jrhahn/rs-smarthome-nodes/cad/export/wohnzimmer_lid.step

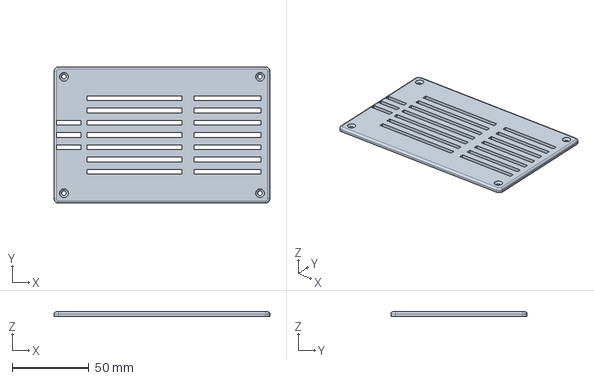
[picture p15: CAD file, 2026-09-13]
cad/export/wohnzimmer_lid.step
141.0 x 89.0 x 3.00 mm
