jrhahn/rs-smarthome-nodes/cad/export/wohnzimmer_tray.step

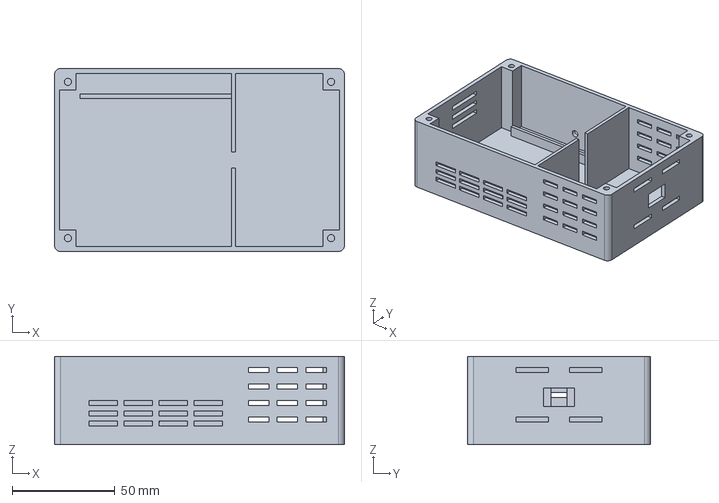
[picture p16: CAD file, 2026-09-13]
cad/export/wohnzimmer_tray.step
141.0 x 89.0 x 43.0 mm
