jrhahn/rs-smarthome-nodes/cad/export/climate_lid.step

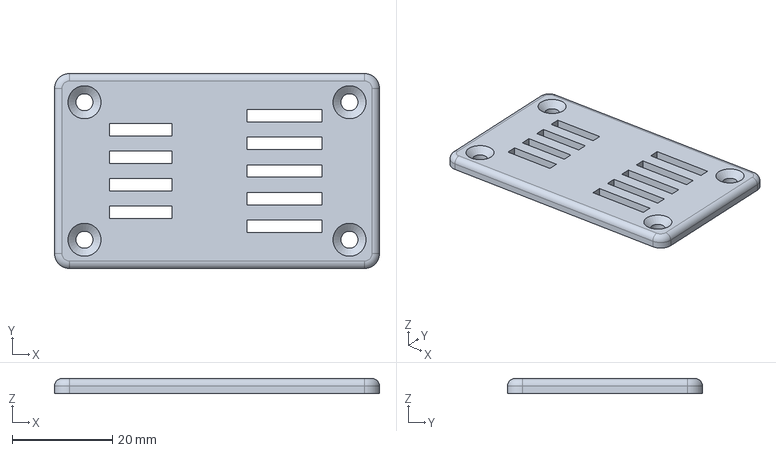
[picture p17: CAD file, 2026-09-13]
cad/export/climate_lid.step
65.0 x 39.0 x 3.00 mm
