jrhahn/rs-smarthome-nodes/cad/export/climate_tray.step

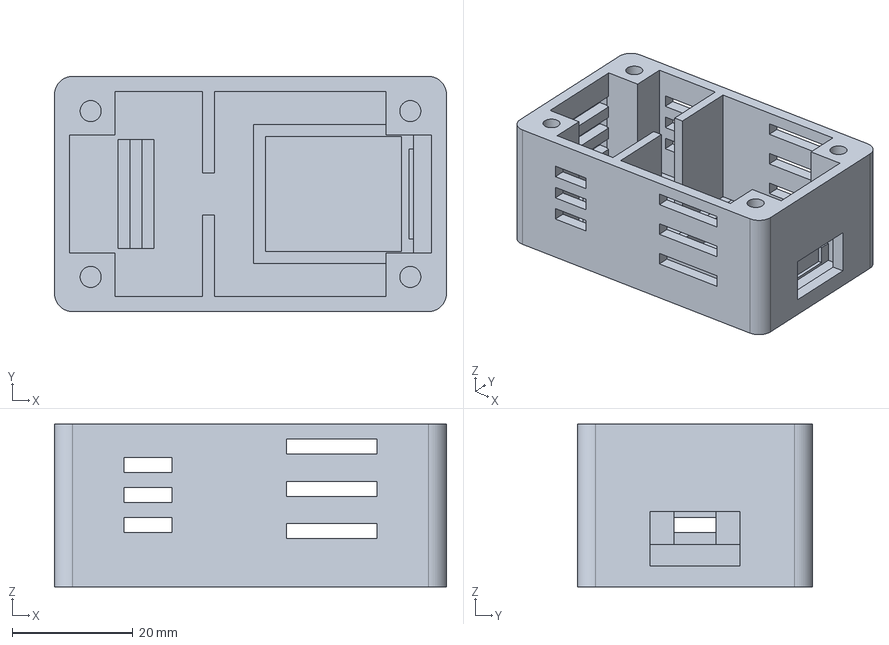
[picture p18: CAD file, 2026-09-13]
cad/export/climate_tray.step
65.0 x 39.0 x 27.0 mm
