jrhahn/rs-smarthome-nodes/src/state.rs

//! Tiny persistent state kept in RTC fast RAM.
//!
//! The firmware polls the scale by cold-booting out of deep sleep on a short
//! interval, so plain statics (in regular RAM) are wiped on every wake. The
//! tare baseline and the presence edge must instead survive across deep sleep,
//! which is exactly what `#[ram(unstable(rtc_fast, persistent))]` gives us: the startup
//! code leaves the region alone instead of zeroing it.
//!
//! **Nothing here may depend on the region being cleared when power is
//! removed.** Discovery used to: it was gated on a "have I announced yet" bit,
//! on the assumption that a cold power-on zeroes RTC RAM. On 2026-09-09 a
//! `wohnzimmer` node had its USB unplugged for several seconds and came back
//! with the bit still set, so its four SDS011 entities stayed unannounced
//! through a reflash, a reset *and* that power cycle — the readings were on the
//! broker the whole time with nothing in Home Assistant to receive them. The
//! board's rails evidently decay slower than the RTC domain forgets.
//!
//! So `FLAGS == 0` is a hint, not a guarantee. See [`discovery_tag`] for the
//! shape that stays correct when the hint is wrong.

use esp_hal::ram;

use crate::sensors::scale;

/// Last known empty-house reading, in raw HX711 ticks.
#[ram(unstable(rtc_fast, persistent))]
static mut BASELINE: i32 = 0;

/// Packed status bits; see `FLAG_*`.
#[ram(unstable(rtc_fast, persistent))]
static mut FLAGS: u32 = 0;

/// Empty-house idle wake-ups accumulated since the last publish. Drives the
/// periodic heartbeat: once it reaches `Config::heartbeat_wakes()` the firmware
/// publishes temperature + weight even without a visitor, then resets it. Any
/// real publish (bird arrived / left) also resets it, so the heartbeat clock
/// restarts from the last time Home Assistant already got a fresh reading.
#[ram(unstable(rtc_fast, persistent))]
static mut IDLE_WAKES: u32 = 0;

/// Consecutive rounds a load has been on the scale, for the stuck-load bound
/// in [`crate::presence::STUCK_AFTER_SECS`]. Reset by an arrival or a
/// departure, so it only ever counts one uninterrupted stretch.
#[ram(unstable(rtc_fast, persistent))]
static mut PRESENT_ROUNDS: u32 = 0;

/// Consecutive rounds the reading has sat in `Decision::Unexplained`, for the
/// recovery bound in [`crate::presence::UNEXPLAINED_ADOPT_AFTER_SECS`]. Reset
/// by every other verdict, so it only ever counts one uninterrupted stretch —
/// the same discipline as [`PRESENT_ROUNDS`], and for the same reason: an
/// occasional odd reading between quiet ones is not a stuck baseline.
#[ram(unstable(rtc_fast, persistent))]
static mut UNEXPLAINED_ROUNDS: u32 = 0;

/// A coarse wall clock in milliseconds, kept across deep sleep as a pair of
/// words because RTC RAM is addressed in `u32`.
///
/// Not read from any counter. It is *re-anchored* by every successful NTP sync
/// -- which happens on every publish round, so at most ten minutes apart -- and
/// between anchors it simply accrues the sleep intervals the node asked for.
/// Bridging ten minutes that way is accurate to a few seconds, where reading
/// the RTC counter would have meant reaching into esp-hal's clock internals for
/// no better answer.
///
/// Zero means "never synced", and readers must treat it as unknown rather than
/// as 1970. This is not a second timestamp source: `clock` explains why
/// stamping a reading from a drifting clock is worse than not stamping it, and
/// that argument stands. The only consumer is the night cadence, which asks an
/// hour-wide question and tolerates minutes of error.
#[ram(unstable(rtc_fast, persistent))]
static mut CLOCK_MS_LO: u32 = 0;
#[ram(unstable(rtc_fast, persistent))]
static mut CLOCK_MS_HI: u32 = 0;

/// Digest of the discovery messages last successfully announced from this
/// board; see [`crate::discovery::announcement_tag`]. Zero means "nothing".

#[ram(unstable(rtc_fast, persistent))]
static mut DISCOVERY_TAG: u32 = 0;

/// Visits counted since the board last lost power entirely.
///
/// Counted at the *arrival*, not at the publish, which is the whole point of
/// keeping it here rather than deriving it in Home Assistant: state topics go
/// out at QoS0 without retain, and `presence_publish_allowed` deliberately
/// drops arrivals that fall inside the 60 s rate limit. Both would undercount,
/// silently, and a bird that comes back twice in half a minute is two visits.
///
/// RTC RAM rather than the flash blob on purpose. A visit is a frequent event —
/// 75 of them on 2026-09-11 — and a flash write means erasing a sector, so
/// counting in flash would spend the sector's endurance on nothing. Losing the
/// total when the cell is swapped is the accepted cost: the entity is
/// `total_increasing`, and Home Assistant treats a drop to zero as a counter
/// reset rather than as negative consumption, so the long-term history it has
/// already recorded survives the board forgetting.
#[ram(unstable(rtc_fast, persistent))]
static mut VISIT_COUNT: u32 = 0;

/// Companion to [`VISIT_COUNT`], holding it XORed with
/// [`scale::VISITS_MAGIC`]. The pair is what makes the counter survivable: a
/// word that has just been added to the firmware comes up holding leftover
/// memory, and a reflash is not a cold boot, so there is no moment at which
/// zeroing it would have been reliable. See that constant for the full story.
#[ram(unstable(rtc_fast, persistent))]
static mut VISIT_CHECK: u32 = 0;

/// Set once the baseline has been tared at least once.
const FLAG_INIT: u32 = 1 << 0;
/// Set while weight is above the presence threshold (edge detection).
const FLAG_PRESENT: u32 = 1 << 1;
/// Set at the end of the first boot of a power cycle. RTC RAM is wiped by a
/// cold power-on but survives deep sleep, so an unset flag means "the board was
/// just plugged in", which is the moment someone might be waiting at the serial
/// console.
///
/// It survives a **reflash** too — verified on hardware 2026-08-19, an
/// `espflash flash` plus the reset it performs left these flags standing. Only
/// removing power clears them. So a board that has already booted once will not
/// re-open the console window just because you flashed it.
const FLAG_BOOTED: u32 = 1 << 3;
/// Set by [`crate::panic_reset`] on its way out, so the boot that follows can
/// say *why* it restarted itself. Without it a panic is reported as a plain
/// software reset, which is also what an over-the-air update looks like -- and
/// the two want very different reactions.
const FLAG_PANICKED: u32 = 1 << 4;
/// Set while a battery node is parked on a low cell; see
/// [`crate::battery::should_park`]. Bit 2 is skipped: RTC RAM survives a
/// reflash, so a bit an older image used could still be standing.
const FLAG_PARKED: u32 = 1 << 5;

/// Whether this node is parked on a low cell.
pub fn parked() -> bool {
    flags() & FLAG_PARKED != 0
}

/// Record whether it is.
pub fn set_parked(value: bool) {
    set_flag(FLAG_PARKED, value);
}

/// Whether the last restart was this firmware giving up on itself.
pub fn panicked() -> bool {
    flags() & FLAG_PANICKED != 0
}

/// Record that it was, or that it has been reported.
pub fn set_panicked(value: bool) {
    set_flag(FLAG_PANICKED, value);
}

fn flags() -> u32 {
    // Single-word reads/writes of a `Persistable` primitive; no other execution
    // context touches these, so a raw read/write is sufficient.
    unsafe { core::ptr::addr_of!(FLAGS).read() }
}

fn set_flags(value: u32) {
    unsafe { core::ptr::addr_of_mut!(FLAGS).write(value) }
}

fn set_flag(bit: u32, on: bool) {
    let updated = if on { flags() | bit } else { flags() & !bit };
    set_flags(updated);
}

/// The persisted empty-house baseline.
pub fn baseline() -> i32 {
    unsafe { core::ptr::addr_of!(BASELINE).read() }
}

/// Replace the persisted baseline.
pub fn set_baseline(value: i32) {
    unsafe { core::ptr::addr_of_mut!(BASELINE).write(value) }
}

/// Whether a baseline has ever been established (false only on the first boot).
pub fn is_initialised() -> bool {
    flags() & FLAG_INIT != 0
}

/// Mark the baseline as established.
pub fn mark_initialised() {
    set_flag(FLAG_INIT, true);
}

/// Whether the previous cycle saw weight on the scale.
pub fn bird_present() -> bool {
    flags() & FLAG_PRESENT != 0
}

/// Record whether weight is currently on the scale.
pub fn set_bird_present(present: bool) {
    set_flag(FLAG_PRESENT, present);
}

/// The digest of the discovery messages last announced from this board, or 0.
///
/// Compared against [`crate::discovery::announcement_tag`] rather than being a
/// boolean, because *any* difference in what Home Assistant should know has to
/// re-announce: a sensor switched on in [`crate::node`] and reflashed, a
/// changed `expire_after`, or RTC RAM that survived a power cycle holding a
/// value from before all of that.
///
/// The boolean it replaces could only ever answer "done", which is precisely
/// the answer that cannot be checked — and it was wrong for six days on the
/// living-room node (see the module note). A digest is checkable: if it does
/// not match what this image would send, the announce happens again, and a
/// stale or garbage word fails to match all by itself.
pub fn discovery_tag() -> u32 {
    unsafe { core::ptr::addr_of!(DISCOVERY_TAG).read() }
}

/// Record the digest of the messages that just went out.
pub fn set_discovery_tag(tag: u32) {
    unsafe { core::ptr::addr_of_mut!(DISCOVERY_TAG).write(tag) }
}

/// How many consecutive rounds a load has been on the scale.
pub fn present_rounds() -> u32 {
    unsafe { core::ptr::addr_of!(PRESENT_ROUNDS).read() }
}

/// Replace the consecutive-load counter.
pub fn set_present_rounds(value: u32) {
    unsafe { core::ptr::addr_of_mut!(PRESENT_ROUNDS).write(value) }
}

/// Anchor the coarse clock to a freshly synced wall time.
pub fn set_clock_ms(millis: u64) {
    unsafe {
        core::ptr::addr_of_mut!(CLOCK_MS_LO).write(millis as u32);
        core::ptr::addr_of_mut!(CLOCK_MS_HI).write((millis >> 32) as u32);
    }
}

/// Carry the coarse clock forward by a stretch the node is about to spend, or
/// just spent. A no-op while the clock is unknown -- advancing a zero would
/// invent a time in 1970 and then keep it.
pub fn advance_clock_ms(millis: u64) {
    if let Some(now) = clock_ms() {
        set_clock_ms(now.saturating_add(millis));
    }
}

/// The coarse wall clock, or `None` if it was never set or has stopped being
/// believable.
pub fn clock_ms() -> Option<u64> {
    let millis = unsafe {
        (core::ptr::addr_of!(CLOCK_MS_HI).read() as u64) << 32
            | core::ptr::addr_of!(CLOCK_MS_LO).read() as u64
    };
    crate::clock::is_plausible(millis).then_some(millis)
}

/// How many consecutive rounds the reading has been unexplained.
/// How many consecutive rounds the reading has been unexplained.
pub fn unexplained_rounds() -> u32 {
    unsafe { core::ptr::addr_of!(UNEXPLAINED_ROUNDS).read() }
}

/// Replace the unexplained-streak counter.
pub fn set_unexplained_rounds(value: u32) {
    unsafe { core::ptr::addr_of_mut!(UNEXPLAINED_ROUNDS).write(value) }
}

/// Visits counted since the last full power loss, or zero if the stored pair
/// does not agree -- which is what leftover RTC memory looks like.
pub fn visit_count() -> u32 {
    let value = unsafe { core::ptr::addr_of!(VISIT_COUNT).read() };
    let check = unsafe { core::ptr::addr_of!(VISIT_CHECK).read() };
    scale::visits_from_pair(value, check)
}

/// Replace the visit counter, writing both halves of the pair so the next read
/// trusts it. Every caller that wants to *record* a visit wants [`count_visit`].
pub fn set_visit_count(value: u32) {
    unsafe {
        core::ptr::addr_of_mut!(VISIT_COUNT).write(value);
        core::ptr::addr_of_mut!(VISIT_CHECK).write(scale::visits_check(value));
    }
}

/// Record one arrival. Saturating, so a board left running for years reports a
/// stuck maximum rather than wrapping to zero and looking like a fresh install.
pub fn count_visit() {
    set_visit_count(visit_count().saturating_add(1));
}

/// Idle wake-ups accumulated since the last publish.
pub fn idle_wakes() -> u32 {
    unsafe { core::ptr::addr_of!(IDLE_WAKES).read() }
}

/// Overwrite the idle wake-up counter (e.g. bump on an empty poll, or reset to
/// zero right after a publish).
pub fn set_idle_wakes(value: u32) {
    unsafe { core::ptr::addr_of_mut!(IDLE_WAKES).write(value) }
}

/// Is this the first boot since the board was **powered up** — power actually
/// removed and reapplied — rather than a wake from deep sleep? A reflash or a
/// reset does not count; see [`FLAG_BOOTED`].
pub fn is_cold_boot() -> bool {
    flags() & FLAG_BOOTED == 0
}

/// Record that this power cycle has booted once; every later wake sees it.
pub fn mark_booted() {
    set_flag(FLAG_BOOTED, true);
}

// --- Reset diagnostics -------------------------------------------------------

/// Reset cause of the most recent boot that was **not** an ordinary deep-sleep
/// wake, as the raw `SocResetReason` discriminant. Zero until one happens.
///
/// Latched rather than read live because the two do not line up in time: a
/// battery node wakes some hundreds of times between publishes, so the boot
/// that carries the interesting cause is almost never the boot that gets to
/// talk to the broker. Holding it here means the next publish carries it.
///
/// RTC RAM is exactly the right store for this. A watchdog reset, a brownout
/// and a software reset all leave it intact, so the evidence survives the event
/// it describes; only removing power clears it, and that is a power-on reset —
/// which this then records as itself.
#[ram(unstable(rtc_fast, persistent))]
static mut RESET_REASON: u32 = 0;

/// How many such resets since power was last removed. One alone is ambiguous;
/// a count climbing over days is a node rebooting in a loop nobody has noticed,
/// which is the failure this whole pair exists to make visible.
#[ram(unstable(rtc_fast, persistent))]
static mut RESET_COUNT: u32 = 0;

/// Says the words around it are ours rather than whatever the region held
/// before. See [`crate::reset_reason::EPOCH_TAG`] for why this is not optional.
#[ram(unstable(rtc_fast, persistent))]
static mut RESET_TAG: u32 = 0;

/// Consecutive joins the *stored* Wi-Fi credentials have been refused; see
/// [`crate::wifi::FALLBACK_AFTER`].
///
/// Here rather than in the connection task because a battery node cold-boots
/// every few seconds: a task local was reset before the threshold could ever be
/// reached, so the fallback never fired on the one node that hangs outdoors.
/// [`crate::reset_reason::latch`] clears it on a power-on, which is the
/// "another try" the original comment intended.
#[ram(unstable(rtc_fast, persistent))]
static mut JOIN_REFUSALS: u32 = 0;

/// Consecutive publish rounds that never reached the broker; see
/// [`crate::node::sleep_backoff_factor`].
///
/// Rounds rather than attempts, and that is why it is not [`JOIN_REFUSALS`]
/// read a second time: with an exponential join backoff a single failed round
/// now spends four or five refusals, so that counter measures how hard the
/// round tried and this one measures how many rounds went nowhere. Only the
/// second is a sane thing to stretch a sleep by.
#[ram(unstable(rtc_fast, persistent))]
static mut FAILED_ROUNDS: u32 = 0;

/// Record this boot's reset cause. Call once, early. A deep-sleep wake is the
/// steady state and is ignored, so what stays latched is the last thing that
/// was not routine.
pub fn note_reset(code: u32) {
    unsafe {
        // Cleared on the same two occasions `latch` clears `JOIN_REFUSALS`: a
        // region that was never ours holds whatever the last firmware left
        // there, and a power-on is somebody standing at the board. Letting
        // either survive would have the first round after it sleep at a
        // backoff earned by a previous run -- half an hour, on a battery node.
        if !reset_state_is_ours() || code == crate::reset_reason::POWER_ON {
            core::ptr::addr_of_mut!(FAILED_ROUNDS).write(0);
        }
        let (tag, count, latched, refusals) = crate::reset_reason::latch(
            core::ptr::addr_of!(RESET_TAG).read(),
            core::ptr::addr_of!(RESET_COUNT).read(),
            core::ptr::addr_of!(RESET_REASON).read(),
            core::ptr::addr_of!(JOIN_REFUSALS).read(),
            code,
        );
        core::ptr::addr_of_mut!(RESET_TAG).write(tag);
        core::ptr::addr_of_mut!(RESET_COUNT).write(count);
        core::ptr::addr_of_mut!(RESET_REASON).write(latched);
        core::ptr::addr_of_mut!(JOIN_REFUSALS).write(refusals);
    }
}

/// Consecutive refusals of the stored credentials, across sleeps. Zero if the
/// region is not ours, so a garbage read cannot fake a run of failures.
pub fn join_refusals() -> u32 {
    if !reset_state_is_ours() {
        return 0;
    }
    unsafe { core::ptr::addr_of!(JOIN_REFUSALS).read() }
}

/// Record the running total. Called by the connection task on each outcome.
pub fn set_join_refusals(value: u32) {
    unsafe { core::ptr::addr_of_mut!(JOIN_REFUSALS).write(value) }
}

/// Consecutive rounds that did not reach the broker, across sleeps. Zero if the
/// region is not ours, so a garbage read cannot stretch a sleep.
pub fn failed_rounds() -> u32 {
    if !reset_state_is_ours() {
        return 0;
    }
    unsafe { core::ptr::addr_of!(FAILED_ROUNDS).read() }
}

/// Record the running total. Called once per publish round, on each outcome.
pub fn set_failed_rounds(value: u32) {
    unsafe { core::ptr::addr_of_mut!(FAILED_ROUNDS).write(value) }
}

/// Whether the words hold a history of ours. False before [`note_reset`] has
/// run on a region that was never ours.
fn reset_state_is_ours() -> bool {
    unsafe {
        core::ptr::addr_of!(RESET_TAG).read() == crate::reset_reason::EPOCH_TAG
            && core::ptr::addr_of!(RESET_COUNT).read() <= crate::reset_reason::MAX_PLAUSIBLE_COUNT
    }
}

/// The latched cause, or zero if nothing but deep sleep has happened.
pub fn last_reset() -> u32 {
    if !reset_state_is_ours() {
        return 0;
    }
    unsafe { core::ptr::addr_of!(RESET_REASON).read() }
}

/// How many non-routine resets since power-on.
pub fn reset_count() -> u32 {
    if !reset_state_is_ours() {
        return 0;
    }
    unsafe { core::ptr::addr_of!(RESET_COUNT).read() }
}
