jrhahn/rs-smarthome-nodes/src/config.rs

//! Runtime configuration persisted in flash (NVS sector) and tunable live from
//! Home Assistant over retained MQTT.
//!
//! Historically the tuning knobs (`PRESENCE_THRESHOLD`, poll intervals) were
//! compile-time constants and the gram calibration (`offset` / `scale_factor`)
//! lived in the Home Assistant template. This module moves all of that onto the
//! controller so it can be changed **without reflashing**: HA publishes each
//! value to a retained `<namespace>/<node>/config/<key>` topic, the firmware reads them
//! whenever it is already online for a publish, and stores the result here.
//!
//! Persistence is a single fixed-layout blob in one 4 KiB flash sector, guarded
//! by a magic + version + CRC-32 so a blank or corrupt sector falls back to
//! [`Config::DEFAULT`]. RTC RAM ([`crate::state`]) is deliberately *not* used for
//! this: it is wiped on a cold power-on (battery swap), and calibration must
//! survive that.
//!
//! The blob encoding and [`Config::apply`] are pure and always compiled; only
//! the flash access itself sits behind the `hal` feature, so the layout and the
//! parsing can be unit-tested on the host (see the `tests` module below).

use core::time::Duration as CoreDuration;

#[cfg(feature = "hal")]
use embedded_storage::{ReadStorage, Storage};
use heapless::String;

use crate::sensors::{scd41, sds011};
use crate::solar;

/// Flash byte-offset of the config blob. Matches the `nvs` partition in
/// espflash's default table; we only touch the first sector of it.
const FLASH_OFFSET: u32 = 0x9000;

/// Second sector of the same partition, holding the node-identity override
/// (see [`crate::node`]). Deliberately a *separate* blob: provisioning a board
/// must never be able to disturb the calibration, and the identity is written
/// once in a board's life while the tuning changes all the time.
const NODE_OFFSET: u32 = 0xA000;

/// Third sector: the Wi-Fi credentials (see [`crate::wifi`]). Separate again,
/// and for a sharper reason than the others — this is the one blob whose loss
/// takes a board off the network entirely, so nothing else may share a sector
/// erase with it.
const WIFI_OFFSET: u32 = 0xB000;

/// `"BIRD"` little-endian — marks an initialised blob.
const MAGIC: u32 = 0x4449_5242;
/// Bump when the on-flash layout changes. A version this code does not know
/// reverts to defaults; the one version it does know how to read comes through
/// [`Config::from_bytes`]'s migration instead — see [`V5_LEN`].
const VERSION: u8 = 7;
/// Serialised length: magic(4) + version(1) + pad(3) + fourteen 4-byte fields + crc(4).
const BLOB_LEN: usize = 4 + 4 + 4 * 14 + 4;
/// Where version 6 ended — the twelve fields up to the tare anchor.
const V6_LEN: usize = 4 + 4 + 4 * 12 + 4;

/// Where version 5 ended: the same header and the first ten fields, then its own
/// CRC. Kept so a board that has been running since before the temperature
/// compensation existed keeps its calibration across the upgrade. `offset` and
/// `scale_factor` are measured against a known weight on a still scale, and
/// dropping them to defaults would turn every reading into plausible nonsense
/// until someone noticed and redid the procedure.
const V5_LEN: usize = 4 + 4 + 4 * 10 + 4;

/// All runtime-tunable settings. `f32` calibration fields are compared bitwise
/// for change detection, which is exactly what we want (a re-sent identical
/// value is a no-op and skips the flash write).
#[derive(Clone, Copy, PartialEq)]
pub struct Config {
    /// Raw HX711 reading corresponding to 0 g (the tare zero).
    pub offset: i32,
    /// Raw HX711 ticks per gram.
    pub scale_factor: f32,
    /// Weight, in grams, that counts as "a bird landed".
    pub threshold_grams: f32,
    /// Deep-sleep seconds between polls while the house is empty.
    pub idle_secs: u32,
    /// Deep-sleep seconds between publishes while a bird is present.
    pub active_secs: u32,
    /// Last numeric tare token seen, so a replayed one is not mistaken for a
    /// second press. `0` for the discovered button, which has no token (see
    /// [`Config::apply`]).
    pub tare_token: u32,
    /// When `false`, the firmware never deep-sleeps: it stays awake and keeps
    /// Wi-Fi up in a loop. Meant for bench testing on USB where deep sleep just
    /// churns the serial monitor. Only consulted on a node whose profile sleeps
    /// at all — a node on [`crate::node::PowerProfile::Mains`] stays awake
    /// regardless.
    pub deep_sleep: bool,
    /// Whether the lamp lights at all tonight, from Home Assistant's light
    /// entity. The twilight window and the cell still decide *when* and *how
    /// bright*; this only ever turns the whole evening off.
    pub lamp_enabled: bool,
    /// Home Assistant's brightness slider, 0..=255.
    ///
    /// A **factor on** [`crate::lamp::MAX_DUTY_PCT`], never a replacement for
    /// it: 255 means "as bright as the compiled ceiling allows", not "full
    /// duty". See the ceiling's own note for why that distinction is the whole
    /// point.
    pub lamp_brightness: u8,
    /// Seconds between periodic "heartbeat" publishes: even with no visitor, the
    /// firmware brings Wi-Fi up this often and publishes temperature + weight so
    /// Home Assistant keeps a fresh reading. Realised as a whole number of idle
    /// wake-ups (see [`Config::heartbeat_wakes`]).
    pub heartbeat_secs: u32,
    /// SCD41 temperature offset in hundredths of °C — the self-heating the
    /// sensor subtracts from both its temperature *and* its humidity output.
    /// Stored in hundredths rather than as an `f32` because it is a calibration
    /// figure read off a comparison, not a computed quantity, and 0.01 °C is
    /// already four times finer than the register resolves. Only consulted on a
    /// node carrying an SCD41 (see [`crate::sensors::scd41`]).
    pub scd41_offset_centi: i32,
    /// Hygroscopic-growth constant κ in hundredths, for the SDS011's humidity
    /// correction (see [`crate::sensors::sds011::compensate`]). Tunable at all
    /// because the right value is a property of the aerosol in *your* rooms
    /// rather than of the sensor; `0` switches the correction off. Only
    /// consulted on a node whose SDS011 slot is compensated.
    pub sds011_kappa_centi: u32,
    /// How far the scale's zero moves with air temperature, in hundredths of a
    /// gram per kelvin. `0` — the default — switches the correction off.
    ///
    /// Signed, because which way the zero goes depends on how the mount is
    /// built, and on the terrace node it goes *down* as it cools. Tunable at
    /// all for the same reason as the SDS011's κ: the figure is a property of
    /// *this* mount rather than of the load cell. On a 1 kg cell the terrace
    /// node measured about 10 g/K, some twenty times a decent cell's own
    /// zero-TC spec, which is what says the strain is in the printed clamps
    /// and not in the steel.
    pub temp_coeff_centi: i32,
    /// Air temperature at the last tare, in tenths of a degree, or
    /// [`TARE_TEMP_UNKNOWN`] if no tare has recorded one.
    ///
    /// The correction needs an anchor, and the tare is the only moment the
    /// node knows the zero is right. Storing the temperature *of that moment*
    /// beside `offset` makes the pair describe one physical state, the same
    /// argument that made `retare` re-anchor the presence baseline. It also
    /// makes the feature roll out safely: until a tare has happened under the
    /// new firmware there is no anchor, and the correction stays off however
    /// the coefficient is set.
    pub tare_temp_tenths: i32,
    /// Deep-sleep seconds between polls during the night window, or `0` to poll
    /// at the ordinary [`Config::idle_secs`] around the clock.
    ///
    /// The cheapest saving this node has left, because it costs nothing that
    /// matters: birds do not feed in the dark, and every wake between dusk and
    /// dawn is the node confirming that nothing is happening. At the measured
    /// 6 s cycle and 1 s awake, a night at 5 s is some 5 400 wake-ups for no
    /// information at all.
    ///
    /// It lengthens the *idle* cadence only. An active interval means a visitor
    /// is being watched, which by definition is not the quiet night this is
    /// about.
    pub night_idle_secs: u32,
    /// Daylight kept clear at each end of the night window, in minutes.
    ///
    /// The window itself is not stored: it is sunset and sunrise for the day,
    /// from [`crate::solar`], so it follows the season without anyone editing
    /// it twice a year. This is the one knob over it — how long after dusk the
    /// node stops looking, and how long before dawn it starts again.
    pub night_margin_min: u32,
}

/// `tare_temp_tenths` when no tare has recorded a temperature.
///
/// A sentinel rather than an `Option` because the blob stores fixed-width
/// fields, and `i32::MIN` is -214 748 364.8 °C — outside anything the SHT31 can
/// report by a wide margin, and outside anything that could arrive from a
/// half-written sector that still passed the CRC.
pub const TARE_TEMP_UNKNOWN: i32 = i32::MIN;

/// The largest zero drift the correction will accept, in hundredths of a gram
/// per kelvin. Generous — the terrace mount sits at a tenth of it — but finite,
/// so a mistyped slider cannot turn a few degrees into kilograms.
pub const MAX_TEMP_COEFF_CENTI: i32 = 20_000;

impl Config {
    /// Factory defaults, used on first boot or a corrupt sector. Chosen to match
    /// the historical compile-time constants, except the threshold which is now
    /// expressed in grams.
    pub const DEFAULT: Config = Config {
        offset: 8_388_608, // mid-scale; overwritten by the first tare / calibration
        scale_factor: 420.0,
        threshold_grams: 10.0,
        idle_secs: 2,
        active_secs: 10,
        tare_token: 0,
        // Sleeping by default, for every profile that sleeps at all. A node
        // that stays awake ignores the flag entirely (see `node::PowerProfile`),
        // so this needs no per-node value — which also keeps `DEFAULT` a plain
        // constant now that the node identity is resolved at runtime from flash.
        deep_sleep: true,
        // On and as bright as the ceiling permits. Neither is persisted in the
        // blob — see `the_lamp_knobs_are_deliberately_not_persisted`.
        lamp_enabled: true,
        lamp_brightness: 255,
        heartbeat_secs: 600, // 10 min
        // The sensor's own power-on value, so an un-calibrated node behaves
        // exactly as it did before this knob existed.
        scd41_offset_centi: scd41::DEFAULT_OFFSET_CENTI,
        // Conservative end of the published range for indoor aerosol; see the
        // constant's own note on why this is a starting point, not a
        // calibration.
        sds011_kappa_centi: sds011::KAPPA_CENTI_DEFAULT,
        // Off. The coefficient belongs to one physical mount, so there is no
        // sensible fleet-wide value to guess at, and a wrong one is worse than
        // none: it would move a zero that was not drifting.
        temp_coeff_centi: 0,
        tare_temp_tenths: TARE_TEMP_UNKNOWN,
        // Off, like every other opt-in here: a node whose clock has never
        // been set must behave exactly as it did before this existed.
        night_idle_secs: 0,
        // Half an hour. Birds feed into dusk and start again before full
        // light, so the window is the inside of the night rather than all of
        // it; see `solar::is_night` for why the two errors do not cost the
        // same.
        night_margin_min: 30,
    };

    /// The presence threshold expressed in raw HX711 ticks, i.e. what `main`
    /// compares the load delta against. Clamped to at least 1 tick so a bad
    /// (zero/negative) calibration can never make everything look "present".
    pub fn threshold_ticks(&self) -> i32 {
        let ticks = self.threshold_grams * self.scale_factor;
        if ticks.is_finite() && ticks >= 1.0 {
            ticks as i32
        } else {
            1
        }
    }

    /// The idle cadence for `hour`, which is the night one inside the window.
    ///
    /// `None` means the node does not know what time it is -- no successful NTP
    /// sync since it last lost power -- and then it polls at the day cadence.
    /// That is the safe direction to be wrong in: it costs current, where the
    /// other way costs visitors.
    pub fn idle_interval_at(&self, now_ms: Option<u64>) -> CoreDuration {
        match now_ms {
            Some(ms)
                if self.night_idle_secs > 0
                    && solar::is_night(
                        solar::minute_of_day(ms),
                        solar::day_of_year(ms),
                        self.night_margin_min,
                    ) =>
            {
                CoreDuration::from_secs(self.night_idle_secs.max(1) as u64)
            }
            _ => self.idle_interval(),
        }
    }

    pub fn idle_interval(&self) -> CoreDuration {
        CoreDuration::from_secs(self.idle_secs.max(1) as u64)
    }

    pub fn active_interval(&self) -> CoreDuration {
        CoreDuration::from_secs(self.active_secs.max(1) as u64)
    }

    /// The heartbeat period as a sleep duration. A battery node **without** a
    /// load cell has no presence logic and therefore nothing to poll for, so
    /// every wake-up is already a full publish; this is what it sleeps between
    /// them, rather than the load-cell [`Config::idle_interval`].
    pub fn heartbeat_interval(&self) -> CoreDuration {
        CoreDuration::from_secs(self.heartbeat_secs.max(1) as u64)
    }

    /// Number of idle wake-ups that make up one heartbeat period: after this
    /// many empty-poll cycles, bring Wi-Fi up and publish temperature + weight
    /// even without a visitor. At least 1, so a misconfigured (tiny) interval
    /// still fires every cycle rather than never.
    /// Whole wake-ups of `wake_secs` before the next heartbeat is due.
    ///
    /// Takes the interval rather than reading [`Config::idle_secs`], because
    /// since the night cadence exists those two are not the same number. A
    /// heartbeat counted in day-length rounds while the node sleeps night-length
    /// ones stretches by exactly their ratio: 120 rounds is ten minutes at 5 s
    /// and **ten hours** at 300 s. The node would go dark from dusk to dawn --
    /// no temperature, no battery, no weight -- which is indistinguishable from
    /// the outage this fleet spent two days chasing in September 2026.
    pub fn heartbeat_wakes_at(&self, wake_secs: u32) -> u32 {
        (self.heartbeat_secs / wake_secs.max(1)).max(1)
    }

    /// Seconds this round will sleep, night cadence included. The one number
    /// every other "seconds to rounds" conversion in a round has to agree with.
    pub fn wake_secs_at(&self, now_ms: Option<u64>) -> u32 {
        self.idle_interval_at(now_ms).as_secs() as u32
    }

    /// Whether a `tare` payload is a fresh press rather than an echo of one
    /// already acted on, remembering the token if it is.
    ///
    /// Two ways to ask for a re-zero, both landing here:
    ///
    /// * a discovered Home Assistant *button*, whose payload is a constant —
    ///   every press looks identical, so the caller deletes the retained
    ///   message once it has acted on it;
    /// * a numeric token (the older automation that published a timestamp),
    ///   where a repeat of the same value is a replay, not a new press.
    ///   Remembering the token means that keeps working, and doubles as a
    ///   backstop if the button's retained message ever fails to clear.
    ///
    /// Split out of [`Config::apply`] so the decision stays host-tested while
    /// the measurement that follows it lives where the load cell is.
    pub fn tare_press_is_new(&mut self, value: &str) -> bool {
        if value.is_empty() {
            return false;
        }
        let token = value.parse::<u32>().unwrap_or(0);
        if token != 0 && token == self.tare_token {
            return false;
        }
        self.tare_token = token;
        true
    }

    /// How many raw ticks of the current reading are the mount expanding rather
    /// than something landing on it — the number to subtract before anything
    /// else looks at the sample.
    ///
    /// Returned in *ticks* rather than grams so the correction lands upstream of
    /// everything: the gram conversion in [`Config::write_grams`], the presence
    /// comparison in [`crate::presence::decide`], and the tare baseline that
    /// tracks between visits all work in raw ticks, and correcting each of them
    /// separately would be three chances to disagree. Subtracting once, at the
    /// point the sample is read, keeps them describing the same scale.
    ///
    /// Zero — i.e. no correction at all — whenever the answer would be a guess:
    /// no coefficient set, no tare anchor recorded, no air reading this round,
    /// or a calibration that cannot be trusted to convert grams to ticks. A
    /// missing SHT31 reading is the ordinary one of those: the sensor is on the
    /// same board and does fail, and a correction against air from some other
    /// hour would be worse than leaving the sample alone.
    pub fn drift_ticks(&self, air_tenths: Option<i32>) -> i32 {
        let Some(air) = air_tenths else { return 0 };
        if self.temp_coeff_centi == 0 || self.tare_temp_tenths == TARE_TEMP_UNKNOWN {
            return 0;
        }
        if !self.scale_factor.is_finite() || self.scale_factor <= 0.0 {
            return 0;
        }
        let kelvin = (air - self.tare_temp_tenths) as f32 / 10.0;
        let grams = kelvin * (self.temp_coeff_centi as f32 / 100.0);
        let ticks = grams * self.scale_factor;
        if !ticks.is_finite() {
            return 0;
        }
        // Saturating rather than wrapping: `as i32` on an out-of-range float is
        // already saturating in Rust, and the clamp on the coefficient means it
        // takes an absurd calibration to get here at all.
        let rounded = if ticks >= 0.0 {
            ticks + 0.5
        } else {
            ticks - 0.5
        };
        rounded as i32
    }

    /// Convert a raw HX711 reading to grams using the stored calibration, and
    /// format it as a fixed-point decimal string with one fractional digit
    /// (float-free formatting, matching the DS18B20 path). A non-positive /
    /// non-finite scale factor falls back to the default so we never divide by
    /// zero or emit `inf`.
    pub fn write_grams(&self, buf: &mut heapless::String<16>, raw: i32) {
        let scale = if self.scale_factor.is_finite() && self.scale_factor > 0.0 {
            self.scale_factor
        } else {
            Config::DEFAULT.scale_factor
        };
        let scaled = (raw - self.offset) as f32 * 10.0 / scale;
        // Round to nearest tenth without needing `f32::round` (libm-free).
        let tenths = if scaled >= 0.0 {
            (scaled + 0.5) as i32
        } else {
            (scaled - 0.5) as i32
        };
        if tenths < 0 {
            let _ = buf.push('-');
        }
        let mag = tenths.unsigned_abs();
        use core::fmt::Write;
        let _ = write!(buf, "{}.{}", mag / 10, mag % 10);
    }

    /// Apply one `key=value` pair received from a `<namespace>/<node>/config/<key>`
    /// topic. Returns `true` if it parsed and actually changed a field.
    ///
    /// `tare` is deliberately **not** handled here. It used to be, adopting a
    /// caller-supplied reference as the gram offset, but a re-zero is not a
    /// setting that arrives in a message -- it is a measurement the node has to
    /// go and take, which needs the bus this type cannot reach. The replay
    /// logic that decides whether a press is new still lives here, in
    /// [`Config::tare_press_is_new`]; the measuring is the caller's half.
    pub fn apply(&mut self, key: &str, value: &str) -> bool {
        let before = *self;
        match key {
            "offset" => {
                if let Ok(v) = value.parse::<i32>() {
                    self.offset = v;
                }
            }
            "scale_factor" => {
                if let Ok(v) = value.parse::<f32>() {
                    if v.is_finite() && v > 0.0 {
                        self.scale_factor = v;
                    }
                }
            }
            "threshold" => {
                if let Ok(v) = value.parse::<f32>() {
                    if v.is_finite() && v >= 0.0 {
                        self.threshold_grams = v;
                    }
                }
            }
            "idle_interval" => {
                if let Ok(v) = value.parse::<u32>() {
                    self.idle_secs = v;
                }
            }
            "active_interval" => {
                if let Ok(v) = value.parse::<u32>() {
                    self.active_secs = v;
                }
            }
            "heartbeat_interval" => {
                if let Ok(v) = value.parse::<u32>() {
                    self.heartbeat_secs = v;
                }
            }
            // Home Assistant sends this as degrees ("2.45"); the sensor and the
            // blob want hundredths. Out-of-range values are clamped rather than
            // dropped, matching `scd41::offset_raw` — the slider has already
            // moved, so silently keeping the old value would be the confusing
            // outcome.
            "scd41_temp_offset" => {
                if let Ok(v) = value.parse::<f32>() {
                    if v.is_finite() {
                        let centi = (v * 100.0) as i32;
                        self.scd41_offset_centi = centi.clamp(0, scd41::MAX_OFFSET_CENTI);
                    }
                }
            }
            // Home Assistant sends κ as a plain number ("0.25"); the blob and
            // the correction want hundredths. Clamped rather than dropped, for
            // the same reason as the SCD41 offset above: the slider has moved.
            "sds011_kappa" => {
                if let Ok(v) = value.parse::<f32>() {
                    if v.is_finite() && v >= 0.0 {
                        let centi = (v * 100.0) as u32;
                        self.sds011_kappa_centi = centi.min(sds011::MAX_KAPPA_CENTI);
                    }
                }
            }
            // Home Assistant sends grams per kelvin ("9.9"), signed; the blob
            // wants hundredths. Clamped rather than dropped, same argument as
            // the two above. Note that `0` is a real setting here and not a
            // rejected value: it is how the correction is switched off without
            // losing the tare anchor beside it.
            "temp_coeff" => {
                if let Ok(v) = value.parse::<f32>() {
                    if v.is_finite() {
                        let centi = (v * 100.0) as i32;
                        self.temp_coeff_centi =
                            centi.clamp(-MAX_TEMP_COEFF_CENTI, MAX_TEMP_COEFF_CENTI);
                    }
                }
            }
            // Home Assistant's light entity, which sends the bare words rather
            // than a number. Anything else leaves the lamp as it was: a garbled
            // payload should not switch a light off in the garden.
            "enabled" => match value {
                "ON" | "on" | "true" | "1" => self.lamp_enabled = true,
                "OFF" | "off" | "false" | "0" => self.lamp_enabled = false,
                _ => {}
            },
            // The brightness slider, 0..=255. Clamped rather than dropped, the
            // same argument as the offsets above — the slider has already
            // moved, so keeping the old value would be the confusing answer.
            "brightness" => {
                if let Ok(v) = value.parse::<u32>() {
                    self.lamp_brightness = v.min(255) as u8;
                }
            }
            // Seconds, like the other three intervals. `0` switches the night
            // cadence off without disturbing the window beside it.
            "night_interval" => {
                if let Ok(v) = value.parse::<u32>() {
                    self.night_idle_secs = v;
                }
            }
            // Minutes of daylight held clear either side of the dark window.
            // `solar::is_night` clamps it too; doing it here as well means the
            // stored value is the one the slider shows.
            "night_margin" => {
                if let Ok(v) = value.parse::<u32>() {
                    self.night_margin_min = v.min(180);
                }
            }
            "deep_sleep" => match value {
                "1" | "true" | "on" | "ON" => self.deep_sleep = true,
                "0" | "false" | "off" | "OFF" => self.deep_sleep = false,
                _ => {}
            },
            _ => {}
        }
        *self != before
    }

    // --- Serialisation ------------------------------------------------------
    fn to_bytes(self) -> [u8; BLOB_LEN] {
        let mut b = [0u8; BLOB_LEN];
        b[0..4].copy_from_slice(&MAGIC.to_le_bytes());
        b[4] = VERSION;
        // b[5..8] padding stays zero
        b[8..12].copy_from_slice(&self.offset.to_le_bytes());
        b[12..16].copy_from_slice(&self.scale_factor.to_le_bytes());
        b[16..20].copy_from_slice(&self.threshold_grams.to_le_bytes());
        b[20..24].copy_from_slice(&self.idle_secs.to_le_bytes());
        b[24..28].copy_from_slice(&self.active_secs.to_le_bytes());
        b[28..32].copy_from_slice(&self.tare_token.to_le_bytes());
        b[32..36].copy_from_slice(&(self.deep_sleep as u32).to_le_bytes());
        b[36..40].copy_from_slice(&self.heartbeat_secs.to_le_bytes());
        b[40..44].copy_from_slice(&self.scd41_offset_centi.to_le_bytes());
        b[44..48].copy_from_slice(&self.sds011_kappa_centi.to_le_bytes());
        b[48..52].copy_from_slice(&self.temp_coeff_centi.to_le_bytes());
        b[52..56].copy_from_slice(&self.tare_temp_tenths.to_le_bytes());
        b[56..60].copy_from_slice(&self.night_idle_secs.to_le_bytes());
        b[60..64].copy_from_slice(&self.night_margin_min.to_le_bytes());
        let crc = crc32(&b[0..64]);
        b[64..68].copy_from_slice(&crc.to_le_bytes());
        b
    }

    /// The two fields version 6 added on top of version 5's ten.
    fn v6_extras(b: &[u8; BLOB_LEN], rest: Config) -> Option<Config> {
        Some(Config {
            temp_coeff_centi: i32::from_le_bytes(b[48..52].try_into().ok()?)
                .clamp(-MAX_TEMP_COEFF_CENTI, MAX_TEMP_COEFF_CENTI),
            tare_temp_tenths: i32::from_le_bytes(b[52..56].try_into().ok()?),
            ..rest
        })
    }

    /// The ten fields versions 5 and 6 share, on top of whatever defaults the
    /// caller starts from. Split out so the migration and the current decoder
    /// read the same bytes the same way rather than drifting apart.
    fn common_from_bytes(b: &[u8; BLOB_LEN], rest: Config) -> Option<Config> {
        Some(Config {
            offset: i32::from_le_bytes(b[8..12].try_into().ok()?),
            scale_factor: f32::from_le_bytes(b[12..16].try_into().ok()?),
            threshold_grams: f32::from_le_bytes(b[16..20].try_into().ok()?),
            idle_secs: u32::from_le_bytes(b[20..24].try_into().ok()?),
            active_secs: u32::from_le_bytes(b[24..28].try_into().ok()?),
            tare_token: u32::from_le_bytes(b[28..32].try_into().ok()?),
            deep_sleep: u32::from_le_bytes(b[32..36].try_into().ok()?) != 0,
            heartbeat_secs: u32::from_le_bytes(b[36..40].try_into().ok()?),
            scd41_offset_centi: i32::from_le_bytes(b[40..44].try_into().ok()?),
            sds011_kappa_centi: u32::from_le_bytes(b[44..48].try_into().ok()?)
                .min(sds011::MAX_KAPPA_CENTI),
            ..rest
        })
    }

    fn from_bytes(b: &[u8; BLOB_LEN]) -> Option<Config> {
        if u32::from_le_bytes(b[0..4].try_into().ok()?) != MAGIC {
            return None;
        }
        match b[4] {
            VERSION => {
                if u32::from_le_bytes(b[64..68].try_into().ok()?) != crc32(&b[0..64]) {
                    return None;
                }
                let rest = Config {
                    night_idle_secs: u32::from_le_bytes(b[56..60].try_into().ok()?),
                    night_margin_min: u32::from_le_bytes(b[60..64].try_into().ok()?).min(180),
                    ..Config::DEFAULT
                };
                Config::common_from_bytes(b, Config::v6_extras(b, rest)?)
            }
            // Version 6: everything it stored is still at the same offset, so
            // the calibration *and* the thermal correction come through, and
            // only the night cadence falls to its default -- which is off.
            6 => {
                if u32::from_le_bytes(b[V6_LEN - 4..V6_LEN].try_into().ok()?)
                    != crc32(&b[0..V6_LEN - 4])
                {
                    return None;
                }
                Config::common_from_bytes(b, Config::v6_extras(b, Config::DEFAULT)?)
            }

            // Version 5 in the sector, version 6 in the firmware: the board has
            // just been flashed with this change. Everything version 5 stored is
            // still at the same offset, so the calibration is read back and only
            // the two new fields fall to their defaults — which is "correction
            // off", so the node behaves exactly as it did until someone sets a
            // coefficient and tares.
            //
            // The CRC is checked over version 5's own range, at version 5's own
            // position. The eight bytes past it are whatever the erase left, and
            // they are never read.
            5 => {
                if u32::from_le_bytes(b[V5_LEN - 4..V5_LEN].try_into().ok()?)
                    != crc32(&b[0..V5_LEN - 4])
                {
                    return None;
                }
                Config::common_from_bytes(b, Config::DEFAULT)
            }
            _ => None,
        }
    }
}

/// Load the config from flash, or [`Config::DEFAULT`] if the sector is blank or
/// corrupt. Call this at boot, before the radio is up (flash access is happier
/// with Wi-Fi idle).
#[cfg(feature = "hal")]
pub fn load() -> Config {
    let mut flash = crate::flash();
    let mut buf = [0u8; BLOB_LEN];
    match flash.read(FLASH_OFFSET, &mut buf) {
        Ok(()) => Config::from_bytes(&buf).unwrap_or(Config::DEFAULT),
        Err(_) => Config::DEFAULT,
    }
}

/// Persist the config to flash. Only call this when it actually changed — the
/// underlying `Storage::write` does a full 4 KiB read-erase-write cycle, so it
/// is both slow and finite-wear. `esp-storage` guards the operation with a
/// critical section, so it is safe to run with the radio still up just before
/// deep sleep. Errors are returned for logging; a failed write simply means the
/// change is lost, not corruption.
#[cfg(feature = "hal")]
pub fn store(config: &Config) -> Result<(), &'static str> {
    let mut flash = crate::flash();
    flash
        .write(FLASH_OFFSET, &config.to_bytes())
        .map_err(|_| "nvs write")
}

// --- Node identity blob ------------------------------------------------------
// A board is normally built for one node (`NODE=` at compile time), but it can
// be *provisioned* to another without a rebuild; that override lives here. The
// layout is magic + version + length + the name + CRC-32, same discipline as the
// config blob above: anything that doesn't check out reads back as "no
// override", so a blank or half-written sector simply falls back to the
// build-time identity.

/// `"NODE"` little-endian.
const NODE_MAGIC: u32 = 0x4544_4F4E;
const NODE_VERSION: u8 = 1;
/// Longest node name we can store (`schlafzimmer` is 12).
pub const NODE_NAME_MAX: usize = 16;
/// magic(4) + version(1) + len(1) + pad(2) + name(16) + crc(4).
const NODE_BLOB_LEN: usize = 4 + 4 + NODE_NAME_MAX + 4;

/// Decode an identity blob. `None` for anything that does not check out — a
/// blank sector, an erased one (all `0xFF`), a stale version, a bad CRC or a
/// length that does not fit — which the caller reads as "no override".
fn decode_node_name(b: &[u8; NODE_BLOB_LEN]) -> Option<String<NODE_NAME_MAX>> {
    if u32::from_le_bytes(b[0..4].try_into().ok()?) != NODE_MAGIC || b[4] != NODE_VERSION {
        return None;
    }
    if u32::from_le_bytes(b[24..28].try_into().ok()?) != crc32(&b[0..24]) {
        return None;
    }
    let len = b[5] as usize;
    if len == 0 || len > NODE_NAME_MAX {
        return None;
    }
    let name = core::str::from_utf8(&b[8..8 + len]).ok()?;
    String::try_from(name).ok()
}

/// Encode an identity blob. Rejects a name that cannot be stored rather than
/// truncating it, since a truncated name would name a different node (or none).
fn encode_node_name(name: &str) -> Result<[u8; NODE_BLOB_LEN], &'static str> {
    if name.is_empty() || name.len() > NODE_NAME_MAX {
        return Err("node name length");
    }
    let mut b = [0u8; NODE_BLOB_LEN];
    b[0..4].copy_from_slice(&NODE_MAGIC.to_le_bytes());
    b[4] = NODE_VERSION;
    b[5] = name.len() as u8;
    b[8..8 + name.len()].copy_from_slice(name.as_bytes());
    let crc = crc32(&b[0..24]);
    b[24..28].copy_from_slice(&crc.to_le_bytes());
    Ok(b)
}

/// The provisioned node name, or `None` when this board runs as the identity it
/// was built with.
#[cfg(feature = "hal")]
pub fn load_node_name() -> Option<String<NODE_NAME_MAX>> {
    let mut flash = crate::flash();
    let mut b = [0u8; NODE_BLOB_LEN];
    flash.read(NODE_OFFSET, &mut b).ok()?;
    decode_node_name(&b)
}

/// Persist a node name, so the next boot comes up as that node. Callers should
/// have validated the name first — an unknown one would leave the board falling
/// back to its build-time identity on every boot.
#[cfg(feature = "hal")]
pub fn store_node_name(name: &str) -> Result<(), &'static str> {
    let b = encode_node_name(name)?;
    crate::flash()
        .write(NODE_OFFSET, &b)
        .map_err(|_| "node nvs write")
}

/// Drop the override, returning the board to its build-time identity.
#[cfg(feature = "hal")]
pub fn clear_node_name() -> Result<(), &'static str> {
    crate::flash()
        .write(NODE_OFFSET, &[0u8; NODE_BLOB_LEN])
        .map_err(|_| "node nvs erase")
}

/// Standard CRC-32 (IEEE, reflected, poly `0xEDB88820`).
///
/// Shared with [`crate::ota`], whose bookkeeping blob follows the same
/// magic/version/CRC discipline. Note that `otadata` itself does *not* use this
/// function — the bootloader seeds its CRC differently, see `ota::entry_crc`.
pub(crate) const fn crc32(data: &[u8]) -> u32 {
    let mut crc = 0xFFFF_FFFFu32;
    let mut i = 0;
    while i < data.len() {
        crc ^= data[i] as u32;
        let mut j = 0;
        while j < 8 {
            let mask = (crc & 1).wrapping_neg();
            crc = (crc >> 1) ^ (0xEDB8_8320 & mask);
            j += 1;
        }
        i += 1;
    }
    !crc
}

// Pin the CRC against the canonical check vector at compile time (same tactic as
// the sensor drivers, since the host test harness can't link this crate).
const _: () = {
    assert!(crc32(b"123456789") == 0xCBF4_3926);
    assert!(crc32(&[]) == 0);
};

// Every blob has to fit inside the single 4 KiB sector it is written to; a
// `Storage::write` past the end would silently spill into the next one.
const _: () = {
    assert!(BLOB_LEN <= 0x1000);
    assert!(NODE_BLOB_LEN <= 0x1000);
    assert!(WIFI_BLOB_LEN <= 0x1000);
};

// --- Wi-Fi credential blob ---------------------------------------------------
// Credentials are normally compiled in, but a board can be told different ones
// over the serial console and remember them (see `crate::wifi`). Same discipline
// as the blobs above: anything that does not check out reads back as "nothing
// stored", so the board falls back to what it was built with rather than
// silently losing the network.

/// `"WIFI"` little-endian.
const WIFI_MAGIC: u32 = 0x4946_4957;
const WIFI_VERSION: u8 = 1;
/// 802.11 caps an SSID at 32 bytes.
pub const SSID_MAX: usize = 32;
/// A WPA2 passphrase is at most 63 characters; a raw PSK is 64 hex digits.
pub const PSK_MAX: usize = 64;
/// magic(4) + version(1) + ssid_len(1) + psk_len(1) + pad(1) + ssid + psk + crc(4).
const WIFI_BLOB_LEN: usize = 8 + SSID_MAX + PSK_MAX + 4;
const WIFI_SSID_AT: usize = 8;
const WIFI_PSK_AT: usize = WIFI_SSID_AT + SSID_MAX;
const WIFI_CRC_AT: usize = WIFI_PSK_AT + PSK_MAX;

/// Decode a credential blob into `(ssid, psk)`. `None` for a blank or erased
/// sector, a stale version, a bad CRC, lengths that do not fit, or bytes that
/// are not UTF-8.
fn decode_credentials(b: &[u8; WIFI_BLOB_LEN]) -> Option<(String<SSID_MAX>, String<PSK_MAX>)> {
    if u32::from_le_bytes(b[0..4].try_into().ok()?) != WIFI_MAGIC || b[4] != WIFI_VERSION {
        return None;
    }
    if u32::from_le_bytes(b[WIFI_CRC_AT..WIFI_BLOB_LEN].try_into().ok()?)
        != crc32(&b[0..WIFI_CRC_AT])
    {
        return None;
    }
    let (ssid_len, psk_len) = (b[5] as usize, b[6] as usize);
    // An empty SSID names no network; an empty passphrase is a legitimate open
    // one, so only the SSID has a lower bound.
    if ssid_len == 0 || ssid_len > SSID_MAX || psk_len > PSK_MAX {
        return None;
    }
    let ssid = core::str::from_utf8(&b[WIFI_SSID_AT..WIFI_SSID_AT + ssid_len]).ok()?;
    let psk = core::str::from_utf8(&b[WIFI_PSK_AT..WIFI_PSK_AT + psk_len]).ok()?;
    Some((String::try_from(ssid).ok()?, String::try_from(psk).ok()?))
}

/// Encode a credential blob. Rejects anything that will not fit rather than
/// truncating — a truncated SSID names a different network, and a truncated
/// passphrase simply never authenticates.
fn encode_credentials(ssid: &str, psk: &str) -> Result<[u8; WIFI_BLOB_LEN], &'static str> {
    if ssid.is_empty() || ssid.len() > SSID_MAX {
        return Err("ssid length");
    }
    if psk.len() > PSK_MAX {
        return Err("psk length");
    }
    let mut b = [0u8; WIFI_BLOB_LEN];
    b[0..4].copy_from_slice(&WIFI_MAGIC.to_le_bytes());
    b[4] = WIFI_VERSION;
    b[5] = ssid.len() as u8;
    b[6] = psk.len() as u8;
    b[WIFI_SSID_AT..WIFI_SSID_AT + ssid.len()].copy_from_slice(ssid.as_bytes());
    b[WIFI_PSK_AT..WIFI_PSK_AT + psk.len()].copy_from_slice(psk.as_bytes());
    let crc = crc32(&b[0..WIFI_CRC_AT]);
    b[WIFI_CRC_AT..WIFI_BLOB_LEN].copy_from_slice(&crc.to_le_bytes());
    Ok(b)
}

/// The stored credentials, or `None` when this board uses the ones it was built
/// with.
#[cfg(feature = "hal")]
pub fn load_credentials() -> Option<(String<SSID_MAX>, String<PSK_MAX>)> {
    let mut flash = crate::flash();
    let mut b = [0u8; WIFI_BLOB_LEN];
    flash.read(WIFI_OFFSET, &mut b).ok()?;
    decode_credentials(&b)
}

/// Persist credentials, so the next boot joins with them.
#[cfg(feature = "hal")]
pub fn store_credentials(ssid: &str, psk: &str) -> Result<(), &'static str> {
    let b = encode_credentials(ssid, psk)?;
    crate::flash()
        .write(WIFI_OFFSET, &b)
        .map_err(|_| "wifi nvs write")
}

/// Drop the stored credentials, returning the board to its build-time ones.
#[cfg(feature = "hal")]
pub fn clear_credentials() -> Result<(), &'static str> {
    crate::flash()
        .write(WIFI_OFFSET, &[0u8; WIFI_BLOB_LEN])
        .map_err(|_| "wifi nvs erase")
}

#[cfg(test)]
mod tests {
    use super::*;

    /// A config that differs from `DEFAULT` in every field, so a serialisation
    /// bug that drops or transposes one shows up.
    ///
    /// Two of those fields are not serialised at all — see
    /// [`sample_after_round_trip`] — and they are set here anyway, so that the
    /// exclusion is asserted somewhere rather than assumed everywhere.
    fn sample() -> Config {
        Config {
            offset: -12_345,
            scale_factor: 512.5,
            threshold_grams: 7.5,
            idle_secs: 3,
            active_secs: 11,
            tare_token: 99,
            deep_sleep: false,
            heartbeat_secs: 1234,
            scd41_offset_centi: 245,
            sds011_kappa_centi: 62,
            temp_coeff_centi: -990,
            tare_temp_tenths: 191,
            night_idle_secs: 300,
            night_margin_min: 45,
            lamp_enabled: false,
            lamp_brightness: 123,
        }
    }

    /// [`sample`] with the two lamp knobs back at their defaults.
    ///
    /// They are the only fields the blob does not carry, so this is what a
    /// round trip is allowed to return. See
    /// [`the_lamp_knobs_are_deliberately_not_persisted`].
    fn sample_after_round_trip() -> Config {
        Config {
            lamp_enabled: Config::DEFAULT.lamp_enabled,
            lamp_brightness: Config::DEFAULT.lamp_brightness,
            ..sample()
        }
    }

    /// [`sample`] as version 6 wrote it: twelve fields and a CRC at byte 56,
    /// with the three ranges version 7 added left as the erase leaves them.
    fn v6_bytes(cfg: Config) -> [u8; BLOB_LEN] {
        let mut b = [0xFFu8; BLOB_LEN];
        let v7 = cfg.to_bytes();
        b[..V6_LEN - 4].copy_from_slice(&v7[..V6_LEN - 4]);
        b[4] = 6;
        let crc = crc32(&b[0..V6_LEN - 4]);
        b[V6_LEN - 4..V6_LEN].copy_from_slice(&crc.to_le_bytes());
        b
    }

    /// The same settings as [`sample`], serialised the way version 5 wrote
    /// them: ten fields and a CRC at byte 48, with the two bytes ranges version
    /// 6 added left as the flash erase leaves them.
    fn v5_bytes(cfg: Config) -> [u8; BLOB_LEN] {
        let mut b = [0xFFu8; BLOB_LEN];
        b[0..4].copy_from_slice(&MAGIC.to_le_bytes());
        b[4] = 5;
        b[5..8].copy_from_slice(&[0, 0, 0]);
        b[8..12].copy_from_slice(&cfg.offset.to_le_bytes());
        b[12..16].copy_from_slice(&cfg.scale_factor.to_le_bytes());
        b[16..20].copy_from_slice(&cfg.threshold_grams.to_le_bytes());
        b[20..24].copy_from_slice(&cfg.idle_secs.to_le_bytes());
        b[24..28].copy_from_slice(&cfg.active_secs.to_le_bytes());
        b[28..32].copy_from_slice(&cfg.tare_token.to_le_bytes());
        b[32..36].copy_from_slice(&(cfg.deep_sleep as u32).to_le_bytes());
        b[36..40].copy_from_slice(&cfg.heartbeat_secs.to_le_bytes());
        b[40..44].copy_from_slice(&cfg.scd41_offset_centi.to_le_bytes());
        b[44..48].copy_from_slice(&cfg.sds011_kappa_centi.to_le_bytes());
        let crc = crc32(&b[0..48]);
        b[48..52].copy_from_slice(&crc.to_le_bytes());
        b
    }

    // --- Config blob --------------------------------------------------------

    #[test]
    fn config_blob_round_trips() {
        for (cfg, expected) in [
            (Config::DEFAULT, Config::DEFAULT),
            (sample(), sample_after_round_trip()),
        ] {
            let decoded = Config::from_bytes(&cfg.to_bytes()).expect("valid blob");
            assert!(decoded == expected);
        }
    }

    /// The lamp's two knobs are **not** in the blob, and that is a decision
    /// rather than an omission.
    ///
    /// Their retained MQTT topics already are the store: Home Assistant holds
    /// the slider, the broker holds the message, and the node reads it back on
    /// the next connect. Spending a blob version and a flash write on a second
    /// copy would buy only the gap between a cold boot and that connect — and
    /// in that gap `MAX_DUTY_PCT` and `charge_permille` are both still in
    /// force, so the worst case is an evening at the ceiling rather than at
    /// whatever the slider said.
    #[test]
    fn the_lamp_knobs_are_deliberately_not_persisted() {
        let cfg = sample();
        assert_ne!(cfg.lamp_enabled, Config::DEFAULT.lamp_enabled);
        assert_ne!(cfg.lamp_brightness, Config::DEFAULT.lamp_brightness);

        let decoded = Config::from_bytes(&cfg.to_bytes()).expect("valid blob");
        assert_eq!(decoded.lamp_enabled, Config::DEFAULT.lamp_enabled);
        assert_eq!(decoded.lamp_brightness, Config::DEFAULT.lamp_brightness);
        // Everything else still survives, or this test would be hiding a bug
        // in the serialiser rather than documenting a choice.
        assert_eq!(decoded.night_margin_min, cfg.night_margin_min);
        assert_eq!(decoded.offset, cfg.offset);
    }

    #[test]
    fn config_blob_rejects_blank_and_erased_sectors() {
        // A never-written sector reads as zeroes on some parts and as 0xFF
        // (erased flash) on others; both must fall back to defaults.
        assert!(Config::from_bytes(&[0x00; BLOB_LEN]).is_none());
        assert!(Config::from_bytes(&[0xFF; BLOB_LEN]).is_none());
    }

    #[test]
    fn config_blob_rejects_a_stale_version() {
        let mut b = sample().to_bytes();
        b[4] = VERSION.wrapping_add(1);
        assert!(Config::from_bytes(&b).is_none());
    }

    #[test]
    fn config_blob_rejects_any_single_bit_flip() {
        // Every byte the CRC covers, and every bit of it. A flip must never
        // decode as a *different valid* config — that would silently move the
        // calibration.
        let good = sample().to_bytes();
        for byte in 0..BLOB_LEN {
            for bit in 0..8 {
                let mut b = good;
                b[byte] ^= 1 << bit;
                assert!(
                    Config::from_bytes(&b).is_none(),
                    "bit {bit} of byte {byte} decoded despite corruption"
                );
            }
        }
    }

    #[test]
    fn config_blob_rejects_a_half_written_sector() {
        // Power lost mid-write: a prefix of the new blob, the rest still erased.
        let good = sample().to_bytes();
        for kept in 1..BLOB_LEN {
            let mut b = [0xFFu8; BLOB_LEN];
            b[..kept].copy_from_slice(&good[..kept]);
            assert!(Config::from_bytes(&b).is_none(), "accepted {kept} bytes");
        }
    }

    #[test]
    fn a_version_5_sector_keeps_its_calibration() {
        // The upgrade this migration exists for: a board that has been weighing
        // birds since before the correction existed must come up with the same
        // zero and the same factor, not with the defaults.
        let old = sample();
        let decoded = Config::from_bytes(&v5_bytes(old)).expect("version 5 is readable");
        assert_eq!(decoded.offset, old.offset);
        assert_eq!(decoded.scale_factor, old.scale_factor);
        assert_eq!(decoded.threshold_grams, old.threshold_grams);
        assert_eq!(decoded.heartbeat_secs, old.heartbeat_secs);
        assert_eq!(decoded.scd41_offset_centi, old.scd41_offset_centi);
        assert_eq!(decoded.sds011_kappa_centi, old.sds011_kappa_centi);
    }

    #[test]
    fn a_migrated_sector_comes_up_with_the_correction_off() {
        // The safe half of the migration. There is no anchor temperature in a
        // version 5 blob and no honest way to invent one, so the node must
        // behave exactly as it did until someone tares under the new firmware.
        let decoded = Config::from_bytes(&v5_bytes(sample())).expect("version 5 is readable");
        assert_eq!(decoded.temp_coeff_centi, 0);
        assert_eq!(decoded.tare_temp_tenths, TARE_TEMP_UNKNOWN);
        assert_eq!(decoded.drift_ticks(Some(250)), 0);
    }

    #[test]
    fn a_corrupt_version_5_sector_is_still_rejected() {
        // The migration must not become a hole in the CRC: the old blob is
        // checked over the old range, at the old position.
        let good = v5_bytes(sample());
        for byte in 0..V5_LEN {
            for bit in 0..8 {
                let mut b = good;
                b[byte] ^= 1 << bit;
                assert!(
                    Config::from_bytes(&b).is_none(),
                    "bit {bit} of byte {byte} decoded despite corruption"
                );
            }
        }
    }

    #[test]
    fn a_version_6_sector_keeps_calibration_and_compensation() {
        // The upgrade path that matters this time: a node that has been
        // temperature-compensating for days must not lose its coefficient or,
        // worse, its anchor — the pair is what makes the correction mean
        // anything, and half of it would be silently wrong.
        let old = sample();
        let decoded = Config::from_bytes(&v6_bytes(old)).expect("version 6 is readable");
        assert_eq!(decoded.offset, old.offset);
        assert_eq!(decoded.scale_factor, old.scale_factor);
        assert_eq!(decoded.temp_coeff_centi, old.temp_coeff_centi);
        assert_eq!(decoded.tare_temp_tenths, old.tare_temp_tenths);
        // And the night cadence comes up off, like every other opt-in.
        assert_eq!(decoded.night_idle_secs, 0);
    }

    #[test]
    fn a_corrupt_version_6_sector_is_still_rejected() {
        let good = v6_bytes(sample());
        for byte in 0..V6_LEN {
            for bit in 0..8 {
                let mut b = good;
                b[byte] ^= 1 << bit;
                assert!(
                    Config::from_bytes(&b).is_none(),
                    "bit {bit} of byte {byte} decoded despite corruption"
                );
            }
        }
    }

    // --- Night cadence ------------------------------------------------------

    #[test]
    fn an_unknown_clock_keeps_the_day_cadence() {
        // Costing current is the safe direction to be wrong in; costing
        // visitors is not.
        let cfg = Config {
            night_idle_secs: 300,
            idle_secs: 5,
            ..Config::DEFAULT
        };
        assert_eq!(cfg.idle_interval_at(None), cfg.idle_interval());
    }

    #[test]
    fn the_night_cadence_applies_only_inside_the_window() {
        let cfg = Config {
            night_idle_secs: 300,
            night_margin_min: 30,
            idle_secs: 5,
            ..Config::DEFAULT
        };
        // 2026-09-26T00:00Z, where sunset is about 17:15 UTC and sunrise 05:15.
        let midnight = 1_790_380_800_000u64;
        assert_eq!(
            cfg.idle_interval_at(Some(midnight + 2 * 3_600_000))
                .as_secs(),
            300
        );
        assert_eq!(
            cfg.idle_interval_at(Some(midnight + 12 * 3_600_000))
                .as_secs(),
            5
        );
    }

    #[test]
    fn a_zero_night_interval_switches_the_whole_thing_off() {
        let cfg = Config {
            night_idle_secs: 0,
            idle_secs: 5,
            ..Config::DEFAULT
        };
        let midnight = 1_790_380_800_000u64;
        for h in 0..24u64 {
            assert_eq!(
                cfg.idle_interval_at(Some(midnight + h * 3_600_000))
                    .as_secs(),
                5,
                "{h}:00"
            );
        }
    }

    // --- Temperature compensation -------------------------------------------

    #[test]
    fn no_coefficient_means_no_correction() {
        let cfg = Config {
            temp_coeff_centi: 0,
            tare_temp_tenths: 190,
            ..Config::DEFAULT
        };
        assert_eq!(cfg.drift_ticks(Some(120)), 0);
    }

    #[test]
    fn no_anchor_means_no_correction() {
        // The coefficient alone is not enough: without the temperature the zero
        // was taken at, "how far has it drifted" has no answer.
        let cfg = Config {
            temp_coeff_centi: 990,
            tare_temp_tenths: TARE_TEMP_UNKNOWN,
            ..Config::DEFAULT
        };
        assert_eq!(cfg.drift_ticks(Some(120)), 0);
    }

    #[test]
    fn a_silent_sensor_means_no_correction() {
        // Rather than the last figure, or a guess at room temperature. The SHT31
        // sits on the same board as the load cell and does fail; air from
        // another hour would move the zero for no reason.
        let cfg = Config {
            temp_coeff_centi: 990,
            tare_temp_tenths: 190,
            ..Config::DEFAULT
        };
        assert_eq!(cfg.drift_ticks(None), 0);
    }

    #[test]
    fn cooling_below_the_tare_temperature_adds_back_what_it_took() {
        // The terrace numbers: tared at 19.0 °C, 9.9 g/K, 420 ticks/g. At
        // 12.2 °C the mount has taken 6.8 K * 9.9 g/K = 67.3 g off the reading,
        // which is very nearly the -67.0 g the node published that night.
        let cfg = Config {
            temp_coeff_centi: 990,
            tare_temp_tenths: 190,
            scale_factor: 420.0,
            ..Config::DEFAULT
        };
        let ticks = cfg.drift_ticks(Some(122));
        let grams = ticks as f32 / cfg.scale_factor;
        assert!(
            (grams + 67.3).abs() < 0.2,
            "expected about -67.3 g of drift, got {grams} g"
        );
        // Subtracting a negative drift is what puts the zero back where it was.
        let raw = 1_000_000;
        assert!(raw - ticks > raw);
    }

    #[test]
    fn at_the_tare_temperature_nothing_moves() {
        let cfg = Config {
            temp_coeff_centi: 990,
            tare_temp_tenths: 190,
            ..Config::DEFAULT
        };
        assert_eq!(cfg.drift_ticks(Some(190)), 0);
    }

    #[test]
    fn the_correction_is_symmetric_about_the_anchor() {
        // One coefficient, both directions — which is the whole claim the
        // measured warming and cooling branches supported (8.6 g/K against
        // 9.9 g/K). If they had disagreed this would be the wrong model.
        let cfg = Config {
            temp_coeff_centi: 990,
            tare_temp_tenths: 190,
            ..Config::DEFAULT
        };
        for delta in [1i32, 25, 68, 150] {
            assert_eq!(
                cfg.drift_ticks(Some(190 + delta)),
                -cfg.drift_ticks(Some(190 - delta)),
                "delta {delta}"
            );
        }
    }

    #[test]
    fn a_broken_calibration_disables_the_correction() {
        // `write_grams` falls back to the default factor here, but this one must
        // not: a correction computed from a factor we do not believe would be a
        // silent, confident lie, while no correction is just the old behaviour.
        for bad in [0.0f32, -420.0, f32::NAN, f32::INFINITY] {
            let cfg = Config {
                temp_coeff_centi: 990,
                tare_temp_tenths: 190,
                scale_factor: bad,
                ..Config::DEFAULT
            };
            assert_eq!(cfg.drift_ticks(Some(120)), 0, "factor {bad}");
        }
    }

    #[test]
    fn an_absurd_coefficient_is_clamped_rather_than_obeyed() {
        let mut cfg = Config::DEFAULT;
        assert!(cfg.apply("temp_coeff", "100000"));
        assert_eq!(cfg.temp_coeff_centi, MAX_TEMP_COEFF_CENTI);
        assert!(cfg.apply("temp_coeff", "-100000"));
        assert_eq!(cfg.temp_coeff_centi, -MAX_TEMP_COEFF_CENTI);
    }

    #[test]
    fn a_negative_coefficient_survives_the_round_trip() {
        // The terrace mount drifts *down* as it cools, and a sign lost in the
        // blob would double the error instead of removing it.
        let cfg = Config {
            temp_coeff_centi: -990,
            tare_temp_tenths: -55,
            ..Config::DEFAULT
        };
        let decoded = Config::from_bytes(&cfg.to_bytes()).expect("valid blob");
        assert_eq!(decoded.temp_coeff_centi, -990);
        assert_eq!(decoded.tare_temp_tenths, -55);
    }

    // --- Config::apply ------------------------------------------------------

    #[test]
    fn apply_parses_every_key() {
        let mut cfg = Config::DEFAULT;
        assert!(cfg.apply("offset", "-500"));
        assert_eq!(cfg.offset, -500);
        assert!(cfg.apply("scale_factor", "123.5"));
        assert_eq!(cfg.scale_factor, 123.5);
        assert!(cfg.apply("threshold", "42"));
        assert_eq!(cfg.threshold_grams, 42.0);
        assert!(cfg.apply("idle_interval", "7"));
        assert_eq!(cfg.idle_secs, 7);
        assert!(cfg.apply("active_interval", "17"));
        assert_eq!(cfg.active_secs, 17);
        assert!(cfg.apply("heartbeat_interval", "900"));
        assert_eq!(cfg.heartbeat_secs, 900);
        assert!(cfg.apply("deep_sleep", "0"));
        assert!(!cfg.deep_sleep);
        assert!(cfg.apply("sds011_kappa", "0.4"));
        assert_eq!(cfg.sds011_kappa_centi, 40);
    }

    #[test]
    fn kappa_is_clamped_to_its_slider_rather_than_dropped() {
        let mut cfg = Config::DEFAULT;
        assert!(cfg.apply("sds011_kappa", "9.9"));
        assert_eq!(cfg.sds011_kappa_centi, sds011::MAX_KAPPA_CENTI);
        // Zero is a legitimate setting: it switches the correction off.
        assert!(cfg.apply("sds011_kappa", "0"));
        assert_eq!(cfg.sds011_kappa_centi, 0);
        // Nonsense leaves the last good value alone.
        for bad in ["-1", "", "off", "NaN"] {
            assert!(!cfg.apply("sds011_kappa", bad), "{bad}");
            assert_eq!(cfg.sds011_kappa_centi, 0, "{bad}");
        }
    }

    #[test]
    fn apply_reports_no_change_for_a_repeat() {
        // What keeps a retained message, re-delivered on every connect, from
        // rewriting flash for ever.
        let mut cfg = Config::DEFAULT;
        assert!(cfg.apply("idle_interval", "5"));
        assert!(!cfg.apply("idle_interval", "5"));
    }

    #[test]
    fn apply_ignores_unparseable_and_unknown_input() {
        let mut cfg = Config::DEFAULT;
        for (key, value) in [
            ("offset", "not-a-number"),
            ("idle_interval", "-1"), // u32
            ("idle_interval", ""),   //
            ("scale_factor", "0"),   // would divide by zero
            ("scale_factor", "-3"),  // would invert the reading
            ("scale_factor", "NaN"), // parses, but is not finite
            ("scale_factor", "inf"), //
            ("threshold", "-1"),     // negative grams
            ("deep_sleep", "maybe"), //
            ("no_such_key", "1"),    //
            ("", "1"),               //
        ] {
            assert!(!cfg.apply(key, value), "{key}={value:?} was accepted");
        }
        assert!(cfg == Config::DEFAULT);
    }

    #[test]
    fn apply_accepts_every_boolean_spelling() {
        let mut cfg = Config::DEFAULT;
        for value in ["0", "false", "off", "OFF"] {
            cfg.deep_sleep = true;
            assert!(cfg.apply("deep_sleep", value));
            assert!(!cfg.deep_sleep);
        }
        for value in ["1", "true", "on", "ON"] {
            cfg.deep_sleep = false;
            assert!(cfg.apply("deep_sleep", value));
            assert!(cfg.deep_sleep);
        }
    }

    #[test]
    fn every_button_press_counts_as_a_new_tare() {
        let mut cfg = Config::DEFAULT;
        // The discovered button sends a constant payload, so every press must
        // count — it is the caller that stops the retained message repeating.
        assert!(cfg.tare_press_is_new("tare"));
        assert!(cfg.tare_press_is_new("tare"));
    }

    #[test]
    fn a_replayed_token_is_not_a_press_but_a_new_one_is() {
        // The older automation published a timestamp; the same one arriving
        // again is the broker replaying, not a second press.
        let mut cfg = Config::DEFAULT;
        assert!(cfg.tare_press_is_new("1000"));
        assert!(!cfg.tare_press_is_new("1000"));
        assert!(cfg.tare_press_is_new("1001"));
    }

    #[test]
    fn an_empty_payload_is_not_a_press() {
        // How a retained message is deleted — it must not read as a press.
        let mut cfg = Config::DEFAULT;
        assert!(!cfg.tare_press_is_new(""));
    }

    #[test]
    fn a_tare_press_never_moves_the_zero_by_itself() {
        // The regression this guards is the whole point of the split: deciding
        // that a press is new must not, on its own, change the calibration.
        // `offset` is now only written after a burst of readings has been taken
        // and checked (see `main::retare`), so a press arriving while the node
        // cannot measure leaves the stored zero exactly as it was.
        let mut cfg = Config::DEFAULT;
        let before = cfg.offset;
        assert!(cfg.tare_press_is_new("tare"));
        assert_eq!(cfg.offset, before);
        // And it is not reachable through the settings path at all any more.
        assert!(!cfg.apply("tare", "tare"));
        assert_eq!(cfg.offset, before);
    }

    // --- Derived values -----------------------------------------------------

    #[test]
    fn threshold_ticks_never_collapses_to_zero() {
        // A zero threshold would make every sample look like a bird.
        let mut cfg = Config::DEFAULT;
        cfg.threshold_grams = 0.0;
        assert_eq!(cfg.threshold_ticks(), 1);
        cfg.threshold_grams = 10.0;
        cfg.scale_factor = f32::NAN;
        assert_eq!(cfg.threshold_ticks(), 1);
        cfg.scale_factor = 100.0;
        assert_eq!(cfg.threshold_ticks(), 1000);
    }

    #[test]
    fn a_scaleless_battery_node_sleeps_the_heartbeat_not_the_idle_poll() {
        // The regression this guards is a battery one: with no load cell every
        // wake-up is a publish with a Wi-Fi connect, so sleeping `idle_secs`
        // (2 s) between them would flatten the cell in hours.
        let cfg = Config::DEFAULT;
        assert_eq!(cfg.heartbeat_interval().as_secs(), 600);
        assert!(cfg.heartbeat_interval() > cfg.idle_interval());
    }

    #[test]
    fn the_heartbeat_interval_never_collapses_to_zero() {
        let mut cfg = Config::DEFAULT;
        cfg.heartbeat_secs = 0;
        assert_eq!(cfg.heartbeat_interval().as_secs(), 1);
    }

    #[test]
    fn the_heartbeat_counts_in_the_rounds_actually_slept() {
        // The defect this guards: at the night cadence the same heartbeat is
        // due after the same *time*, not after the same number of wakes.
        let cfg = Config {
            heartbeat_secs: 600,
            idle_secs: 5,
            night_idle_secs: 300,
            ..Config::DEFAULT
        };
        assert_eq!(cfg.heartbeat_wakes_at(5), 120);
        assert_eq!(cfg.heartbeat_wakes_at(300), 2);
        // Same elapsed time either way, which is the whole point.
        assert_eq!(
            cfg.heartbeat_wakes_at(5) * 5,
            cfg.heartbeat_wakes_at(300) * 300
        );
    }

    #[test]
    fn the_round_length_follows_the_night_cadence() {
        let cfg = Config {
            idle_secs: 5,
            night_idle_secs: 300,
            night_margin_min: 30,
            ..Config::DEFAULT
        };
        let midnight = 1_790_380_800_000u64;
        assert_eq!(cfg.wake_secs_at(Some(midnight + 2 * 3_600_000)), 300);
        assert_eq!(cfg.wake_secs_at(Some(midnight + 12 * 3_600_000)), 5);
        assert_eq!(cfg.wake_secs_at(None), 5);
    }

    #[test]
    fn heartbeat_wakes_is_at_least_one() {
        let mut cfg = Config::DEFAULT;
        // A zero interval would divide by zero; it clamps to one second, so the
        // heartbeat still lands on its configured period.
        cfg.idle_secs = 0;
        assert_eq!(cfg.heartbeat_wakes_at(cfg.idle_secs), cfg.heartbeat_secs);
        cfg.idle_secs = 2;
        cfg.heartbeat_secs = 600;
        assert_eq!(cfg.heartbeat_wakes_at(cfg.idle_secs), 300);
        cfg.heartbeat_secs = 1; // shorter than one wake
        assert_eq!(cfg.heartbeat_wakes_at(cfg.idle_secs), 1);
    }

    #[test]
    fn write_grams_formats_fixed_point() {
        let mut cfg = Config::DEFAULT;
        cfg.offset = 0;
        cfg.scale_factor = 100.0;
        for (raw, expected) in [
            (0, "0.0"),
            (1000, "10.0"),
            (1005, "10.1"), // rounds away from zero
            (-1005, "-10.1"),
            (-50, "-0.5"),
        ] {
            let mut buf = String::new();
            cfg.write_grams(&mut buf, raw);
            assert_eq!(buf.as_str(), expected, "raw {raw}");
        }
    }

    #[test]
    fn write_grams_survives_a_broken_calibration() {
        // A zero scale factor must not produce `inf` or `NaN` on the wire.
        let mut cfg = Config::DEFAULT;
        cfg.offset = 0;
        cfg.scale_factor = 0.0;
        let mut buf = String::new();
        cfg.write_grams(&mut buf, 4200);
        assert!(buf
            .chars()
            .all(|c| c.is_ascii_digit() || c == '.' || c == '-'));
    }

    // --- Node identity blob -------------------------------------------------

    #[test]
    fn node_blob_round_trips_every_fleet_name() {
        for (name, _) in crate::node::FLEET {
            let blob = encode_node_name(name).expect("encodable");
            assert_eq!(decode_node_name(&blob).as_deref(), Some(*name));
        }
    }

    #[test]
    fn node_blob_rejects_unstorable_names() {
        assert!(encode_node_name("").is_err());
        assert!(encode_node_name(&"x".repeat(NODE_NAME_MAX + 1)).is_err());
        // Exactly full is fine — the boundary the fleet must stay inside.
        assert!(encode_node_name(&"x".repeat(NODE_NAME_MAX)).is_ok());
    }

    #[test]
    fn node_blob_rejects_blank_erased_and_corrupt_sectors() {
        assert!(decode_node_name(&[0x00; NODE_BLOB_LEN]).is_none());
        assert!(decode_node_name(&[0xFF; NODE_BLOB_LEN]).is_none());

        let good = encode_node_name("kueche").unwrap();
        for byte in 0..NODE_BLOB_LEN {
            for bit in 0..8 {
                let mut b = good;
                b[byte] ^= 1 << bit;
                assert!(
                    decode_node_name(&b).is_none(),
                    "bit {bit} of byte {byte} decoded despite corruption"
                );
            }
        }
    }

    #[test]
    fn node_blob_rejects_a_half_written_sector() {
        let good = encode_node_name("schlafzimmer").unwrap();
        for kept in 1..NODE_BLOB_LEN {
            let mut b = [0xFFu8; NODE_BLOB_LEN];
            b[..kept].copy_from_slice(&good[..kept]);
            assert!(decode_node_name(&b).is_none(), "accepted {kept} bytes");
        }
    }

    #[test]
    fn node_blob_rejects_a_length_that_overruns_the_slot() {
        // A length field pointing past the name field, with the CRC recomputed
        // so only the bounds check stands between it and a panic.
        let mut b = encode_node_name("bad").unwrap();
        b[5] = NODE_NAME_MAX as u8 + 1;
        let crc = crc32(&b[0..24]);
        b[24..28].copy_from_slice(&crc.to_le_bytes());
        assert!(decode_node_name(&b).is_none());
    }

    // --- Wi-Fi credential blob ----------------------------------------------

    #[test]
    fn credentials_round_trip() {
        for (ssid, psk) in [
            ("MyNetwork", "hunter2"),
            // An open network, and the two extremes of what can be stored.
            ("OpenNet", ""),
            ("x", "y"),
            (
                "0123456789abcdef0123456789abcdef",
                "0123456789abcdef0123456789abcdef0123456789abcdef0123456789abcdef",
            ),
            // Non-ASCII is legal in an SSID and must survive byte-for-byte.
            ("Küche 2.4␣GHz", "Fußball"),
        ] {
            let blob = encode_credentials(ssid, psk).expect("encodable");
            let (out_ssid, out_psk) = decode_credentials(&blob).expect("valid blob");
            assert_eq!(out_ssid.as_str(), ssid);
            assert_eq!(out_psk.as_str(), psk);
        }
    }

    #[test]
    fn credentials_reject_what_will_not_fit() {
        assert!(encode_credentials("", "psk").is_err());
        assert!(encode_credentials(&"x".repeat(SSID_MAX + 1), "psk").is_err());
        assert!(encode_credentials("Net", &"x".repeat(PSK_MAX + 1)).is_err());
        assert!(encode_credentials(&"x".repeat(SSID_MAX), &"x".repeat(PSK_MAX)).is_ok());
    }

    #[test]
    fn credentials_reject_blank_erased_and_corrupt_sectors() {
        assert!(decode_credentials(&[0x00; WIFI_BLOB_LEN]).is_none());
        assert!(decode_credentials(&[0xFF; WIFI_BLOB_LEN]).is_none());

        // Every bit of every byte. A flip that decoded as *different* valid
        // credentials would take the board off the network with no clue why.
        let good = encode_credentials("MyNetwork", "hunter2").unwrap();
        for byte in 0..WIFI_BLOB_LEN {
            for bit in 0..8 {
                let mut b = good;
                b[byte] ^= 1 << bit;
                assert!(
                    decode_credentials(&b).is_none(),
                    "bit {bit} of byte {byte} decoded despite corruption"
                );
            }
        }
    }

    #[test]
    fn credentials_reject_a_half_written_sector() {
        let good = encode_credentials("MyNetwork", "hunter2").unwrap();
        for kept in 1..WIFI_BLOB_LEN {
            let mut b = [0xFFu8; WIFI_BLOB_LEN];
            b[..kept].copy_from_slice(&good[..kept]);
            assert!(decode_credentials(&b).is_none(), "accepted {kept} bytes");
        }
    }

    #[test]
    fn credentials_reject_lengths_that_overrun_their_fields() {
        // Length fields pointing past their buffers, with the CRC recomputed so
        // only the bounds checks stand between them and a panic.
        for (ssid_len, psk_len) in [(SSID_MAX as u8 + 1, 7), (9, PSK_MAX as u8 + 1), (0, 7)] {
            let mut b = encode_credentials("MyNetwork", "hunter2").unwrap();
            b[5] = ssid_len;
            b[6] = psk_len;
            let crc = crc32(&b[0..WIFI_CRC_AT]);
            b[WIFI_CRC_AT..WIFI_BLOB_LEN].copy_from_slice(&crc.to_le_bytes());
            assert!(
                decode_credentials(&b).is_none(),
                "accepted ssid_len {ssid_len}, psk_len {psk_len}"
            );
        }
    }

    #[test]
    fn credentials_reject_a_stale_version() {
        let mut b = encode_credentials("MyNetwork", "hunter2").unwrap();
        b[4] = WIFI_VERSION.wrapping_add(1);
        assert!(decode_credentials(&b).is_none());
    }

    #[test]
    fn the_three_blobs_live_in_different_sectors() {
        // A 4 KiB erase takes the whole sector with it, so two blobs sharing one
        // would mean re-taring a scale could drop its credentials.
        let sectors = [FLASH_OFFSET, NODE_OFFSET, WIFI_OFFSET];
        for (i, a) in sectors.iter().enumerate() {
            for b in &sectors[i + 1..] {
                assert!(a.abs_diff(*b) >= 0x1000, "{a:#x} and {b:#x} share a sector");
            }
        }
    }
}
